plbogen2/tillandsia/PNGs/blade.png

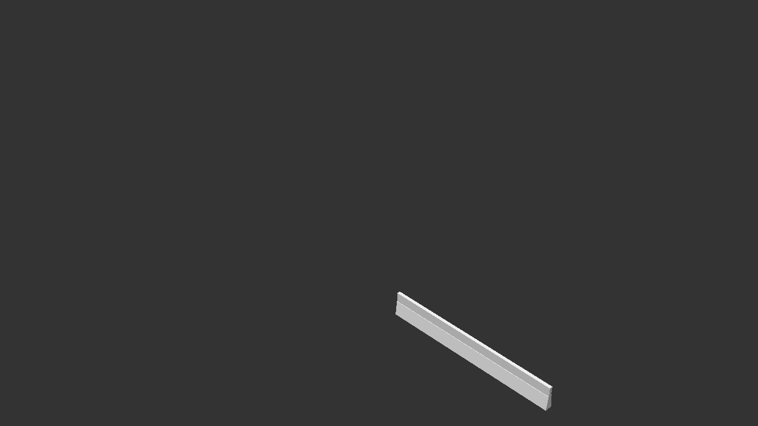
PNGs/blade.png
