plbogen2/tillandsia/PNGs/filter_back.png

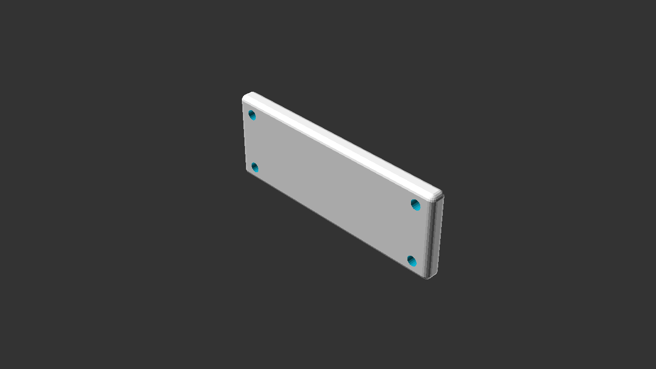
PNGs/filter_back.png
